dylemmas/STSYS32/companion_app/gui/tab_shot_detail.py

"""SHOT DETAIL tab — target plot and coaching."""

from __future__ import annotations

import math
from collections import deque

import numpy as np
import pyqtgraph as pg
from PyQt6.QtCore import QRectF, Qt, QTimer
from PyQt6.QtGui import QColor, QFont, QPainter, QPen, QPainterPath
from PyQt6.QtWidgets import (
    QHBoxLayout,
    QLabel,
    QSplitter,
    QTextEdit,
    QVBoxLayout,
    QWidget,
)

from gui.main_window import DataRouter, MainWindow
from gui.theme import (
    ACCENT,
    BG2,
    BG3,
    BG4,
    BLUE,
    FG,
    FG_DIM,
    ORANGE,
    RED,
    YELLOW,
)
from gui.widgets.score_gauge import ScoreGauge
from stasys.protocol.packets import DataRawSample, EvtShotDetected


class TargetPlot(QWidget):
    """Custom painted target with concentric rings and colored trace overlay."""

    def __init__(self, parent=None) -> None:
        super().__init__(parent)
        self._shot_x: float = 0.0
        self._shot_y: float = 0.0
        self._has_shot = False
        # Trace path: list of (x, y, phase) tuples
        # phase: "hold", "press", "recoil"
        self._trace_points: list[tuple[float, float, str]] = []
        self.setMinimumSize(300, 300)

    def set_shot(self, x: float, y: float) -> None:
        self._shot_x = x
        self._shot_y = y
        self._has_shot = True
        self.update()

    def set_trace(self, points: list[tuple[float, float, str]]) -> None:
        self._trace_points = points
        self.update()

    def clear(self) -> None:
        self._shot_x = 0.0
        self._shot_y = 0.0
        self._has_shot = False
        self._trace_points.clear()
        self.update()

    def paintEvent(self, event) -> None:
        painter = QPainter(self)
        painter.setRenderHint(QPainter.RenderHint.Antialiasing)

        w = self.width()
        h = self.height()
        cx = w / 2
        cy = h / 2
        max_r = min(w, h) * 0.45
        deg_per_pixel = 5.0 / max_r  # 5 degrees full scale

        # Background
        painter.fillRect(0, 0, w, h, QColor(BG2))

        # Concentric rings at 1°, 2°, 3.5°, 5°
        ring_radii = [1.0, 2.0, 3.5, 5.0]
        for r_deg in ring_radii:
            r_px = r_deg * max_r / 5.0
            painter.setPen(QPen(QColor("#333"), 1.0 if r_deg < 3.0 else 1.5))
            painter.drawEllipse(
                int(cx - r_px), int(cy - r_px), int(r_px * 2), int(r_px * 2)
            )
            # Label
            painter.setPen(QColor("#555"))
            painter.setFont(QFont("JetBrains Mono", 8))
            painter.drawText(int(cx + r_px + 4), int(cy + 4), f"{r_deg}°")

        # Crosshair
        painter.setPen(QPen(QColor("#444"), 1.0))
        painter.drawLine(int(cx), 0, int(cx), h)
        painter.drawLine(0, int(cy), w, int(cy))

        # Bullseye center
        painter.setPen(QPen(QColor(ACCENT), 1.5))
        painter.drawEllipse(int(cx - 4), int(cy - 4), 8, 8)

        # Draw trace path with phase coloring
        if self._trace_points:
            phase_colors = {
                "hold": QColor(BLUE).lighter(140),
                "press": QColor(ORANGE).lighter(130),
                "recoil": QColor(RED).lighter(130),
            }
            for i in range(1, len(self._trace_points)):
                x1, y1, phase1 = self._trace_points[i - 1]
                x2, y2, phase2 = self._trace_points[i]
                color = phase_colors.get(phase2, QColor(FG))
                pen = QPen(color, 1.5)
                painter.setPen(pen)
                px1 = cx + x1 * max_r / 5.0
                py1 = cy - y1 * max_r / 5.0
                px2 = cx + x2 * max_r / 5.0
                py2 = cy - y2 * max_r / 5.0
                painter.drawLine(int(px1), int(py1), int(px2), int(py2))

        # Shot impact dot
        if self._has_shot:
            sx = cx + self._shot_x * max_r / 5.0
            sy = cy - self._shot_y * max_r / 5.0
            painter.setBrush(QColor(ACCENT))
            painter.setPen(QPen(QColor(ACCENT), 1.5))
            painter.drawEllipse(int(sx - 6), int(sy - 6), 12, 12)

            # Distance label
            dist = (self._shot_x ** 2 + self._shot_y ** 2) ** 0.5
            painter.setFont(QFont("JetBrains Mono", 8))
            painter.setPen(QColor(FG_DIM))
            painter.drawText(
                int(sx + 8), int(sy - 4),
                f"{dist:.2f}°"
            )
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
