dylemmas/STSYS32/companion_app/tests/test_storage.py

"""Tests for the STASYS storage layer: SessionStore, RawStore, DataLogger, conversions."""

from __future__ import annotations

import tempfile
import time
from pathlib import Path

import numpy as np
import pytest

from stasys.protocol.packets import DataRawSample, EvtShotDetected
from stasys.storage.conversions import (
    imu_accel_gyro_convert,
    imu_accel_magnitude,
    raw_to_accel_ms2,
    raw_to_gyro_dps,
    raw_to_temp_c,
)
from stasys.storage.database import create_database
from stasys.storage.raw_store import RawStore
from stasys.storage.session_store import SessionStore


# =============================================================================
# Conversions
# =============================================================================

class TestConversions:
    def test_raw_to_accel_scalar(self) -> None:
        assert raw_to_accel_ms2(8192) == pytest.approx(9.81, rel=1e-3)
        assert raw_to_accel_ms2(0) == 0.0
        assert raw_to_accel_ms2(-8192) == pytest.approx(-9.81, rel=1e-3)

    def test_raw_to_gyro_scalar(self) -> None:
        assert raw_to_gyro_dps(655) == pytest.approx(10.0, rel=1e-3)
        assert raw_to_gyro_dps(0) == 0.0

    def test_raw_to_temp_scalar(self) -> None:
        assert raw_to_temp_c(0) == pytest.approx(36.53, rel=1e-2)

    def test_imu_accel_gyro_convert_array(self) -> None:
        # 9 columns: timestamp_us, accel_x/y/z, gyro_x/y/z, piezo, temp
        raw = np.array([[0, 8192, 0, 0, 655, 0, 0, 0, 0]], dtype=np.int32)
        converted = imu_accel_gyro_convert(raw)
        assert converted[0, 1] == pytest.approx(9.81, rel=1e-3)  # accel_x
        assert converted[0, 4] == pytest.approx(10.0, rel=1e-3)   # gyro_x

    def test_imu_accel_magnitude(self) -> None:
        raw = np.array([[0, 8192, 8192, 8192, 0, 0, 0, 0, 0]], dtype=np.int32)
        mag = imu_accel_magnitude(raw)
        expected = (9.81 ** 2 * 3) ** 0.5
        assert mag[0] == pytest.approx(expected, rel=1e-3)
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
